Stempell/SkullPad/Photos/Zrzut ekranu 2026-06-29 173110.png

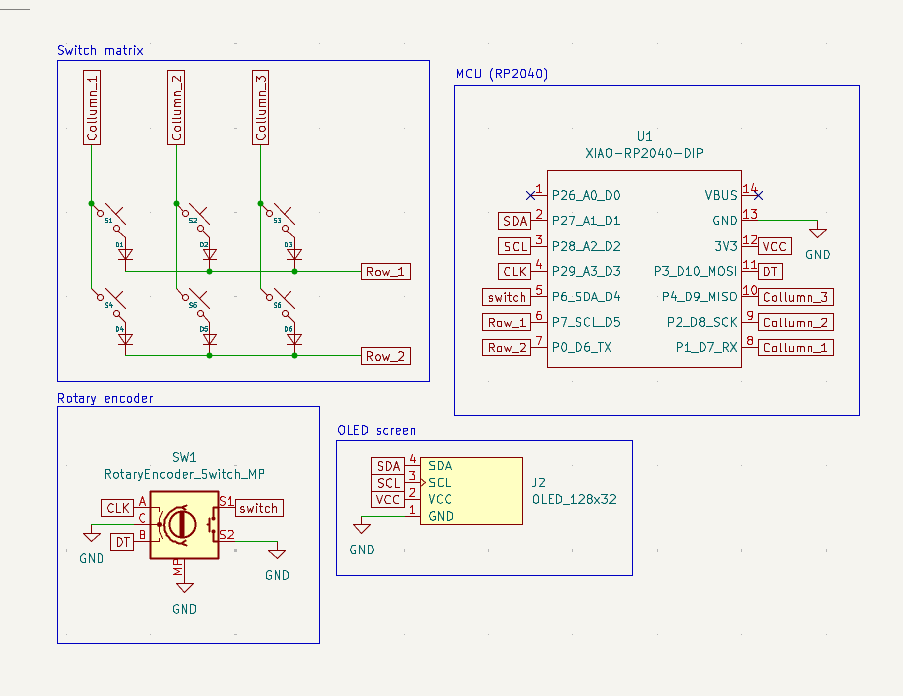
Photos/Zrzut ekranu 2026-06-29 173110.png
