Stempell/SkullPad/Photos/Zrzut ekranu 2026-06-29 214759 — kopia.png

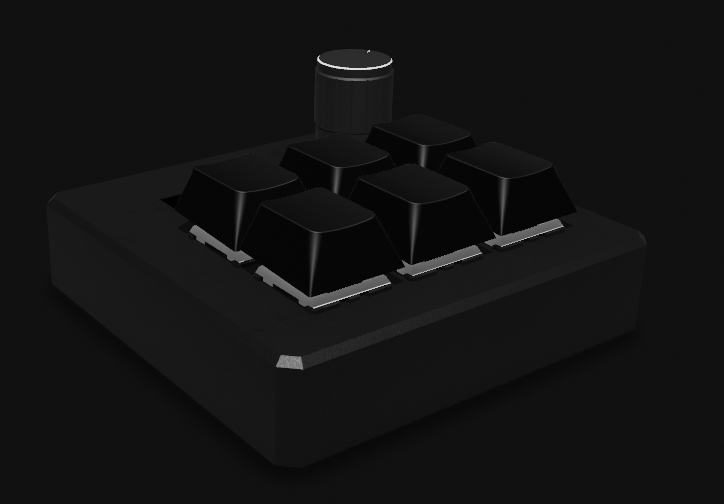
Photos/Zrzut ekranu 2026-06-29 214759 — kopia.png
