Stempell/SkullPad/Photos/Zrzut ekranu 2026-06-29 214826.png

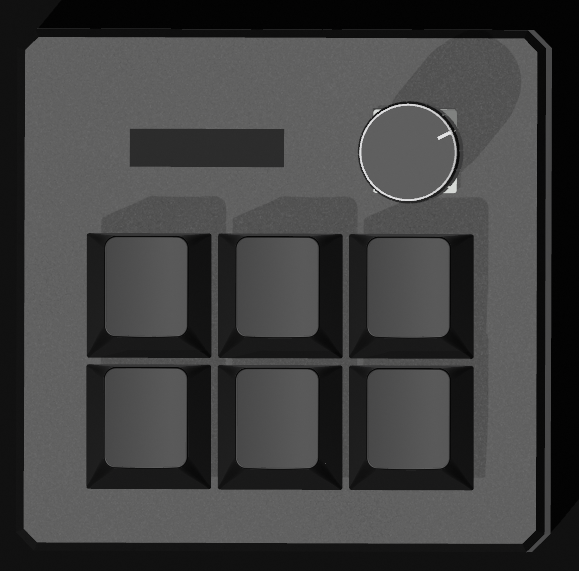
Photos/Zrzut ekranu 2026-06-29 214826.png
