Stempell/SkullPad/Photos/Zrzut ekranu 2026-06-29 221610.png

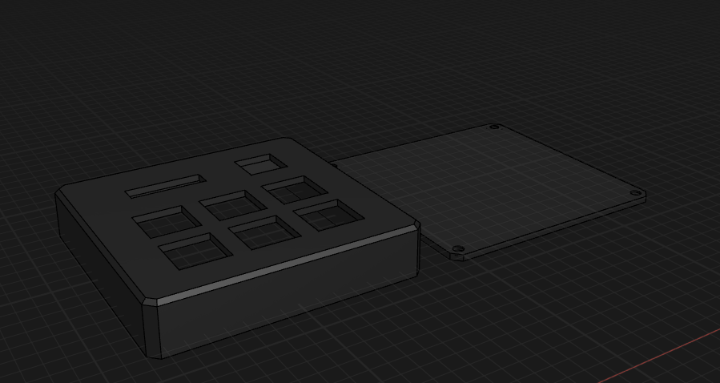
Photos/Zrzut ekranu 2026-06-29 221610.png
