Stempell/SkullPad/Photos/Zrzut ekranu 2026-06-30 004722.png

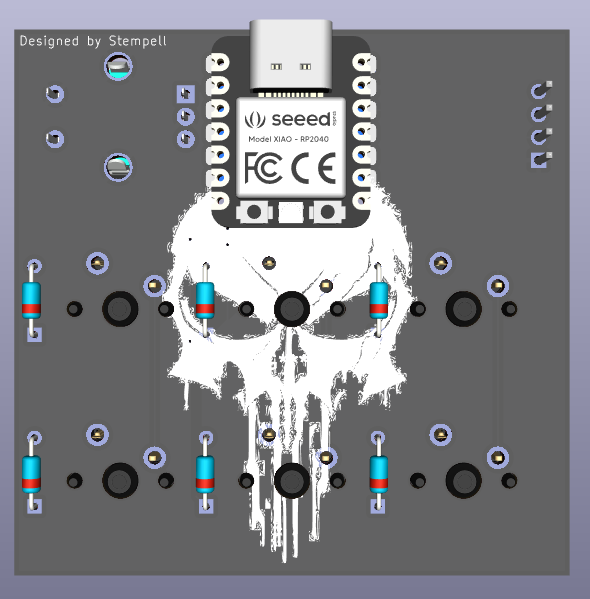
Photos/Zrzut ekranu 2026-06-30 004722.png
