Stempell/SkullPad/Photos/Zrzut ekranu 2026-06-30 160106.png

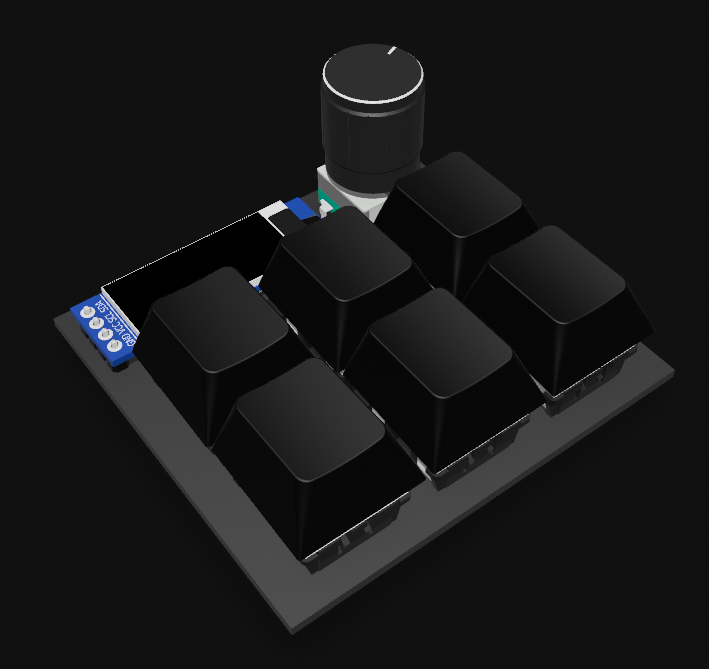
Photos/Zrzut ekranu 2026-06-30 160106.png
